Sebastian-Jaimes/DroneNavigationController/docs/Captura de pantalla 2024-10-26 214837.png

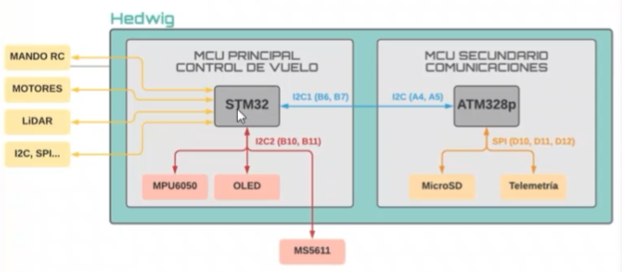
docs/Captura de pantalla 2024-10-26 214837.png
