Sebastian-Jaimes/DroneNavigationController/docs/rect234-4.png

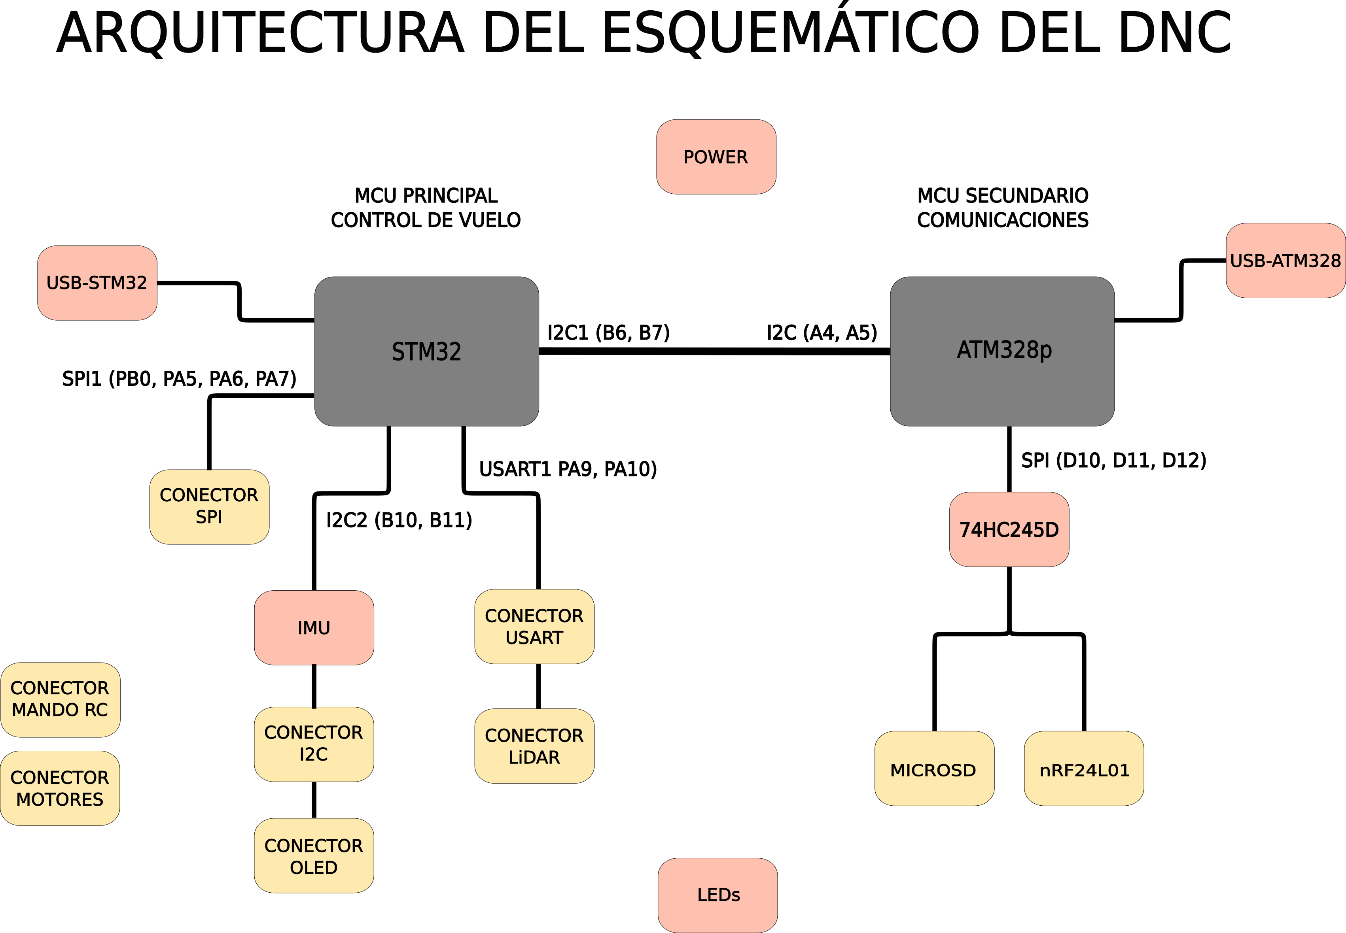
docs/rect234-4.png
