Sebastian-Jaimes/DroneNavigationController/hardware/3d_models/Drone Frame/TopPlate.SLDPRT

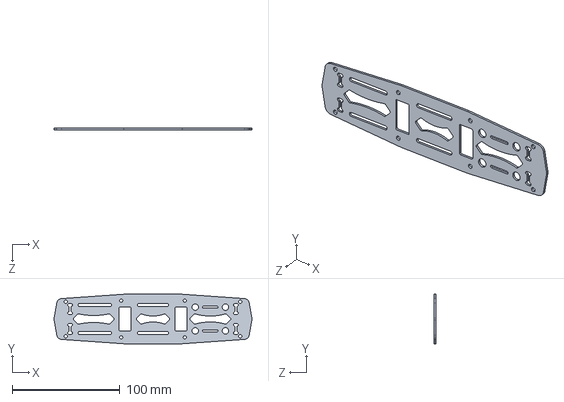
[picture p177: CAD file, 2024-09-07]
hardware/3d_models/Drone Frame/TopPlate.SLDPRT
183.8 x 46.0 x 1.50 mm
