Sebastian-Jaimes/DroneNavigationController/hardware/3d_models/zmr250-quadcopter-frame/DAMPER1.SLDPRT

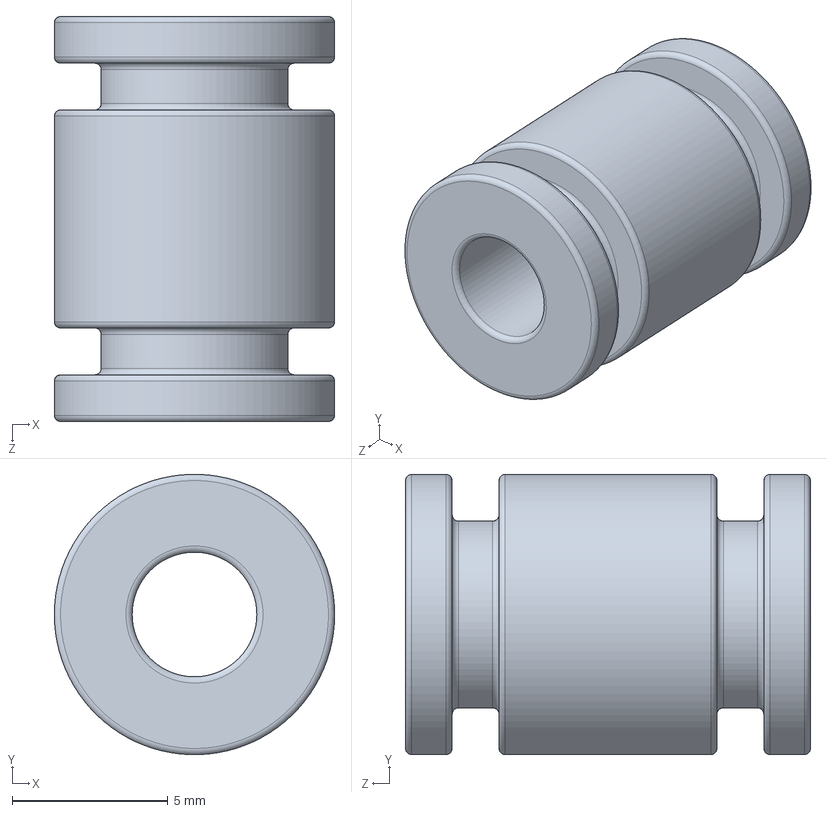
[picture p178: CAD file, 2024-11-21]
hardware/3d_models/zmr250-quadcopter-frame/DAMPER1.SLDPRT
9.00 x 8.99 x 13.0 mm
