Sebastian-Jaimes/DroneNavigationController/hardware/3d_models/3D/0.96 OLED v3.step

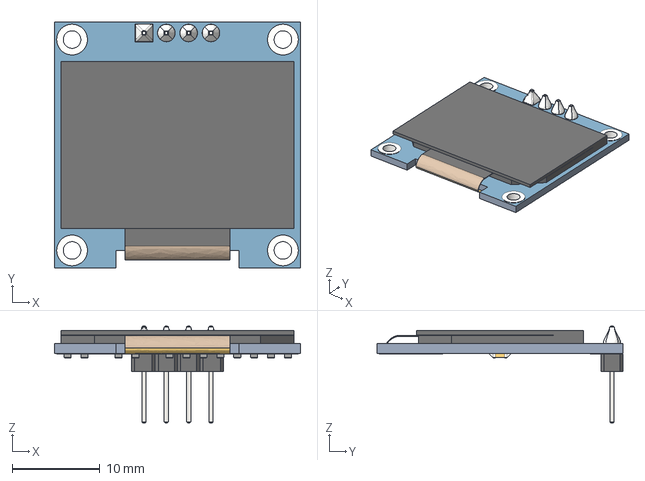
[picture p179: CAD file, 2024-09-07]
hardware/3d_models/3D/0.96 OLED v3.step
28.0 x 28.0 x 11.0 mm
