Sebastian-Jaimes/DroneNavigationController/hardware/3d_models/3D/Crystal_5012_2p_16MHz.stp

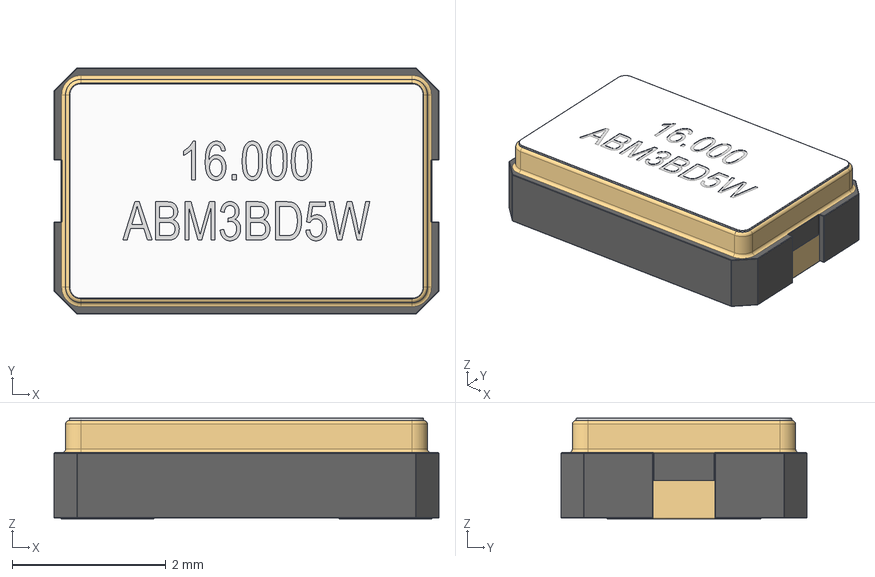
[picture p180: CAD file, 2024-09-07]
hardware/3d_models/3D/Crystal_5012_2p_16MHz.stp
5.00 x 3.20 x 1.31 mm
