Sebastian-Jaimes/DroneNavigationController/hardware/3d_models/3D/USB.STEP

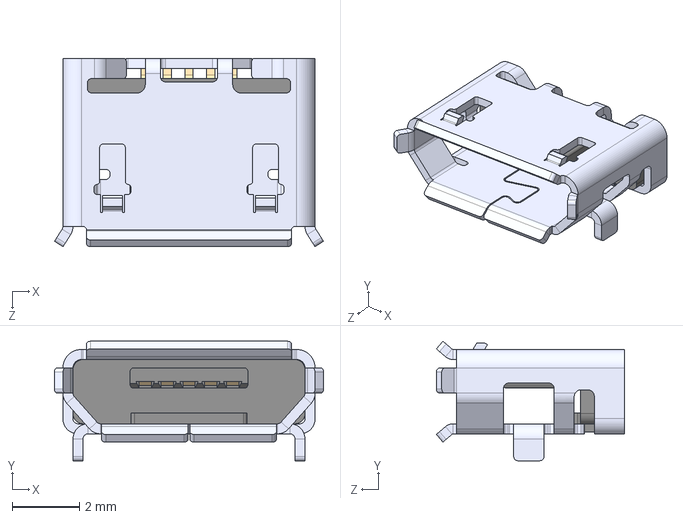
[picture p181: CAD file, 2024-09-07]
hardware/3d_models/3D/USB.STEP
8.00 x 3.55 x 5.60 mm
