Sebastian-Jaimes/DroneNavigationController/hardware/3d_models/Drone Frame/Spacer.SLDPRT

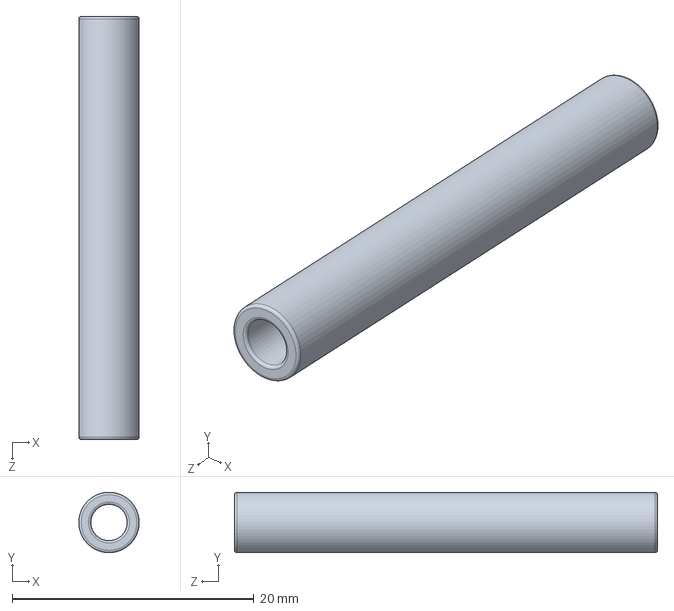
[picture p182: CAD file, 2024-09-07]
hardware/3d_models/Drone Frame/Spacer.SLDPRT
5.00 x 5.00 x 35.0 mm
