Sebastian-Jaimes/DroneNavigationController/hardware/3d_models/3D/SD_472192001.stp

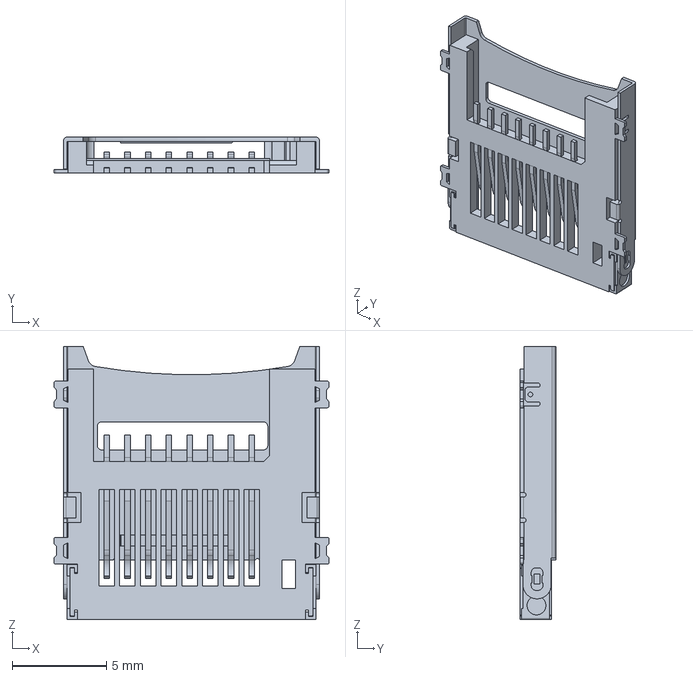
[picture p183: CAD file, 2024-09-07]
hardware/3d_models/3D/SD_472192001.stp
14.6 x 1.90 x 14.5 mm
