Sebastian-Jaimes/DroneNavigationController/hardware/3d_models/3D/LM358DR.STEP

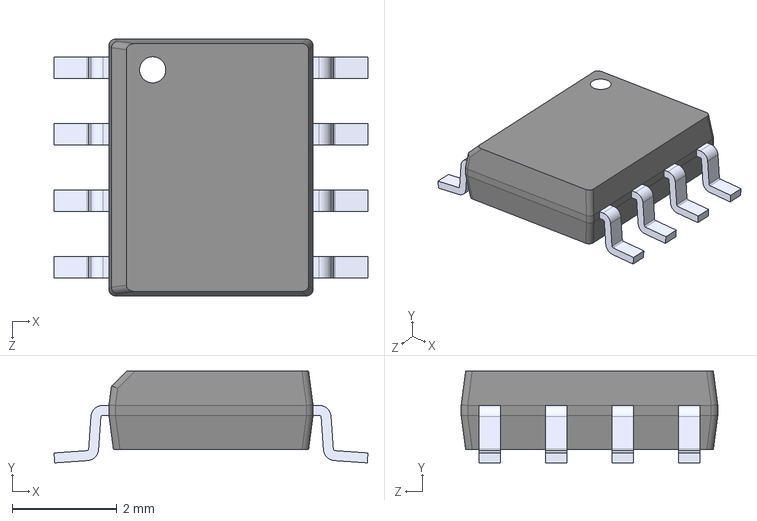
[picture p184: CAD file, 2024-09-07]
hardware/3d_models/3D/LM358DR.STEP
5.99 x 1.75 x 4.90 mm
