Sebastian-Jaimes/DroneNavigationController/hardware/3d_models/zmr250-quadcopter-frame/Rahmen.STEP

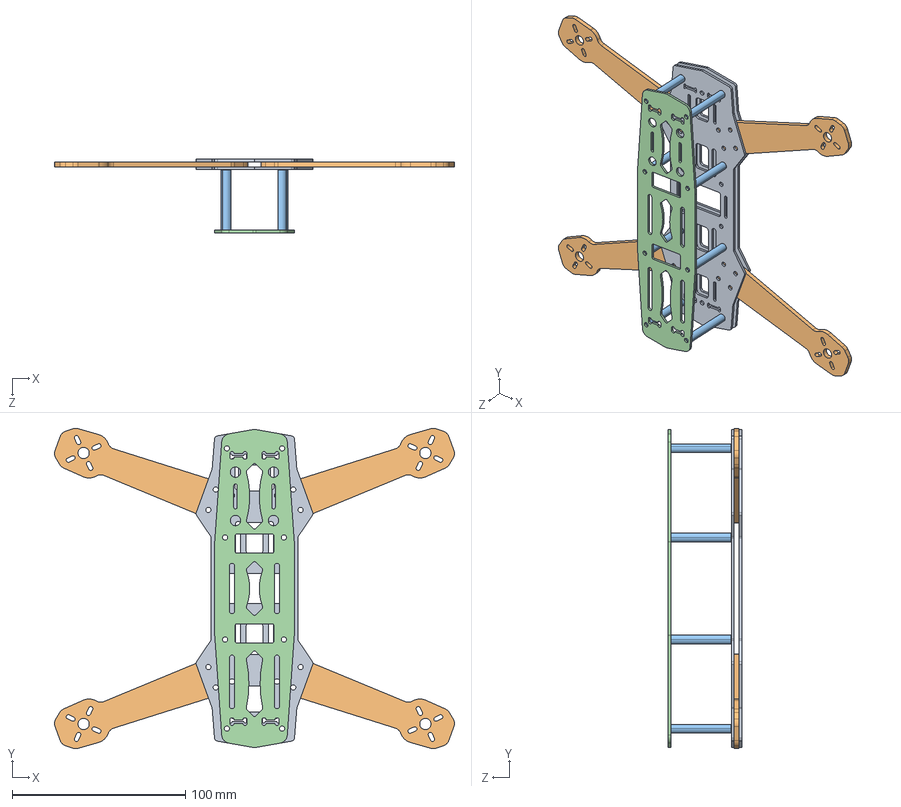
[picture p185: CAD file, 2024-09-07]
hardware/3d_models/zmr250-quadcopter-frame/Rahmen.STEP
231.2 x 185.2 x 42.5 mm
BottomPlate x 2
Arm x 4
Spacer x 8
TopPlate
