Sebastian-Jaimes/DroneNavigationController/hardware/3d_models/3D/Antena_SMA_142-0701-201.step

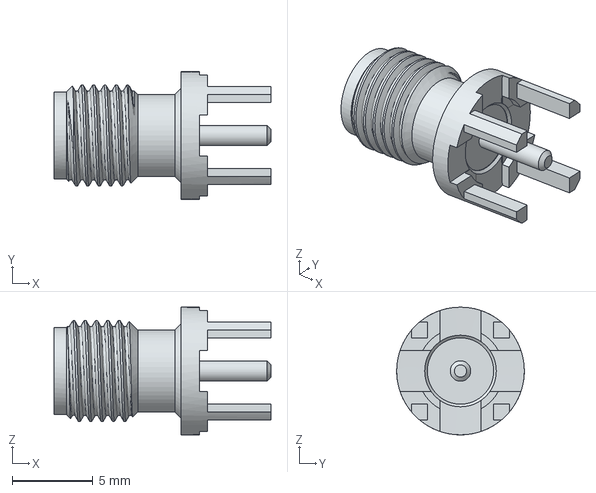
[picture p186: CAD file, 2024-09-07]
hardware/3d_models/3D/Antena_SMA_142-0701-201.step
13.5 x 7.92 x 7.92 mm
