Sebastian-Jaimes/DroneNavigationController/hardware/3d_models/3D/ATMEGA328P-AUR--3DModel-STEP-56544.STEP

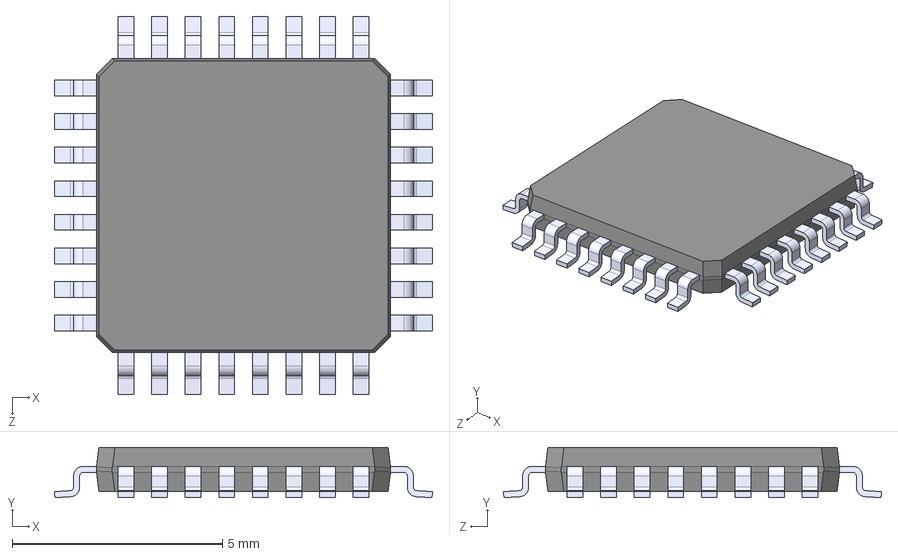
[picture p187: CAD file, 2024-09-07]
hardware/3d_models/3D/ATMEGA328P-AUR--3DModel-STEP-56544.STEP
9.00 x 1.20 x 9.00 mm
