Sebastian-Jaimes/DroneNavigationController/electronics/DNC/modules/ESC.kicad_sch

## KiCad design electronics/DNC/modules/ESC.kicad_sch (2026-10-08)

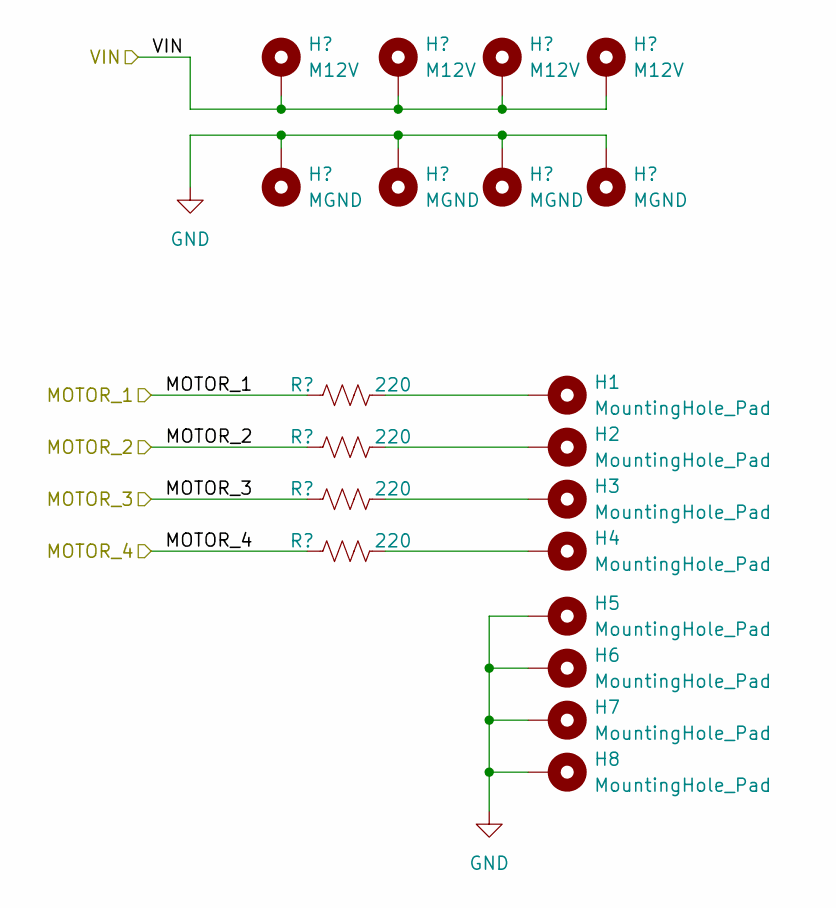
[picture p190: schematic ESC.kicad_sch]

Parts:
H1, H2, H3, H4, H5, H6, H7, H8: MountingHole_Pad

Connections:
GND: H5.1, H6.1, H7.1, H8.1
