Sebastian-Jaimes/DroneNavigationController/electronics/DNC/modules/POWER_MANAGEMENT_SYSTEM.kicad_sch

## KiCad design electronics/DNC/modules/POWER_MANAGEMENT_SYSTEM.kicad_sch (2026-10-08)

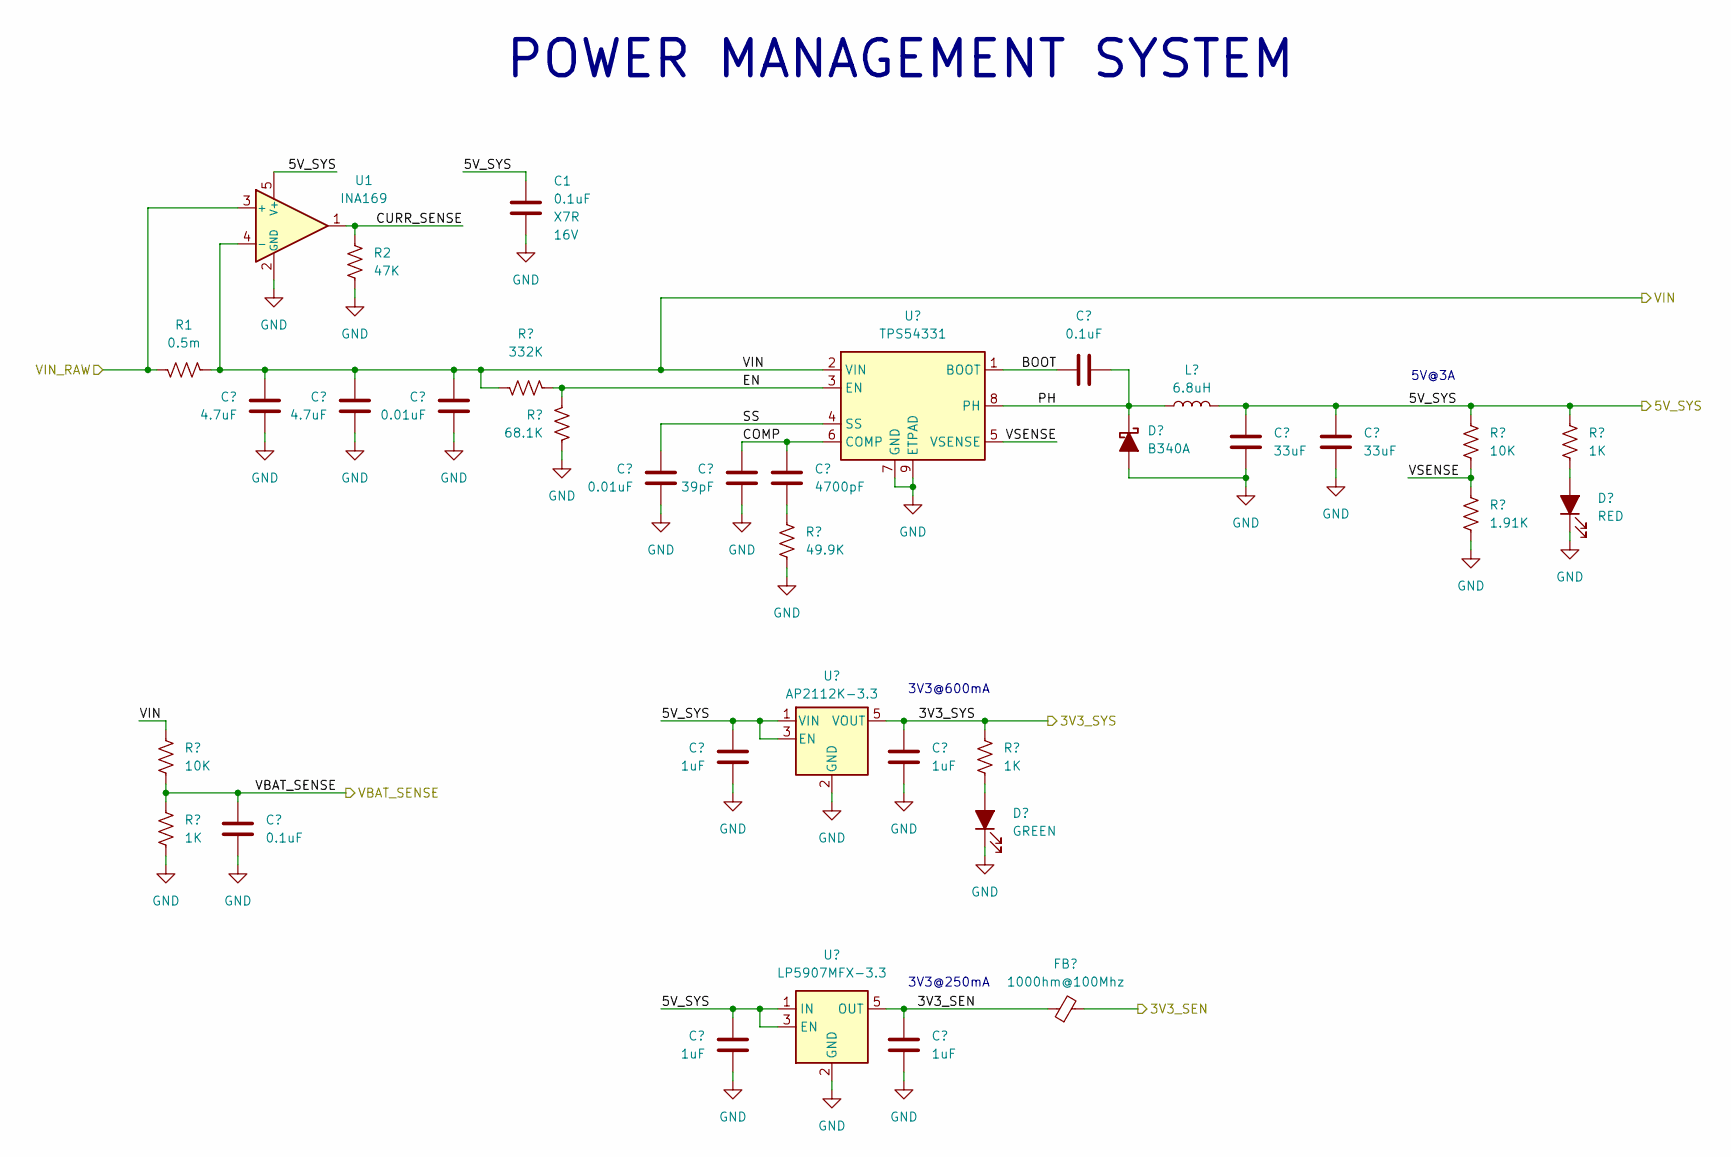
[picture p191: schematic POWER_MANAGEMENT_SYSTEM.kicad_sch]

Parts:
C1: 0.1uF; VOLTAGE 16V
R1: 0.5m; R_2512_6332Metric
R2: 47K
U1: INA169; SOT-23-5

Connections:
5V_SYS: C1.1, U1.5 (V+)
CURR_SENSE: R2.1, U1.1
GND: C1.2, R2.2, U1.2 (GND)
VIN: R1.1, U1.4 (-)
VIN_RAW: R1.2, U1.3 (+)

Notes on the sheet:
3V3@600mA
3V3@250mA
POWER MANAGEMENT SYSTEM
5V@3A
